wiretap-retro/MigStorm-ITX/Firmware/ARM Firmware/ASB140501/ARM/src/menu.c

/*
Copyright 2005, 2006, 2007 Dennis van Weeren
Copyright 2008, 2009 Jakub Bednarski

This file is part of Minimig

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
You should have received a copy of the GNU General Public License
along with this program.  If not, see <http://www.gnu.org/licenses/>.
*/

// 2009-11-14   - OSD labels changed
// 2009-12-15   - added display of directory name extensions
// 2010-01-09   - support for variable number of tracks
// SB:
// 2014-04-24   - added page wide file list scroll at joystick left/right
// 2014-04-30   - added load of alternative FPGA core .BIN file
// 2014-05-01   - added chipset selection via keyboard shortcut
#include "AT91SAM7S256.h"
#include "stdbool.h"
#include "printf.h"
#include "stringlight.h"
#include "errors.h"
#include "MMC.h"
#include "FAT.h"
#include "OSD.h"
#include "FPGA.h"
#include "FDD.h"
#include "HDD.h"
#include "hardware.h"
#include "firmware.h"
#include "config.h"
#include "menu.h"

// time delay after which file/dir name starts to scroll
#define SCROLL_DELAY 500

unsigned long scroll_offset; // file/dir name scrolling position
unsigned long scroll_timer;  // file/dir name scrolling timer

// other constants
#define DIRSIZE 8 // number of items in directory display window

unsigned char menustate = MENU_NONE1;
unsigned char menusub = 0;
unsigned long menu_timer;


extern unsigned char drives;
extern adfTYPE df[4];

extern configTYPE config;
extern fileTYPE file;
extern char s[40];

extern unsigned char fat32;

extern DIRENTRY DirEntry[MAXDIRENTRIES];
extern unsigned char sort_table[MAXDIRENTRIES];
extern unsigned char nDirEntries;
extern unsigned char iSelectedEntry;
extern unsigned long iCurrentDirectory;
extern char DirEntryLFN[MAXDIRENTRIES][261];
char DirEntryInfo[MAXDIRENTRIES][5]; // disk number info of dir entries
char DiskInfo[5]; // disk number info of selected entry

extern const char version[];

const char *config_filter_msg[] =  {"Disabled", "Hor", "Ver", "Hor+Ver"};
const char *config_memory_chip_msg[] = {"0.5 MB", "1.0 MB", "1.5 MB", "2.0 MB"};
const char *config_memory_slow_msg[] = {"0.0 MB", "0.5 MB", "1.0 MB", "1.5 MB"};
const char *config_scanlines_msg[] = {"VGA alike", "TV  alike", "Cache Off"};

char *config_chipset_msg[] = {"OCS-A500", "OCS-A1000", "ECS", ""};

char *config_autofire_msg[] = {"         AUTOFIRE OFF", "         AUTOFIRE FAST", "         AUTOFIRE MEDIUM", "         AUTOFIRE SLOW"};

extern char UploadKickstart(char *name);
extern unsigned char SaveConfiguration(char *filename);

extern unsigned char DEBUG;

unsigned char config_autofire = 0;

// file selection menu variables
char *fs_pFileExt = NULL;
unsigned char fs_Options;
unsigned char fs_MenuSelect;
unsigned char fs_MenuCancel;

void SelectFile(char* pFileExt, unsigned char Options, unsigned char MenuSelect, unsigned char MenuCancel)
{
    // this function displays file selection menu

    if (strncmp(pFileExt, fs_pFileExt, 3) != 0) // check desired file extension
    { // if different from the current one go to the root directory and init entry buffer
        ChangeDirectory(DIRECTORY_ROOT);
        ScanDirectory(SCAN_INIT, pFileExt, Options);
    }

    fs_pFileExt = pFileExt;
    fs_Options = Options;
    fs_MenuSelect = MenuSelect;
    fs_MenuCancel = MenuCancel;

    menustate = MENU_FILE_SELECT1;
}

void HandleUI(void)
{
    unsigned char i, c, up, down, select, menu, right, left;
    unsigned long len;
    static hardfileTYPE t_hardfile[2]; // temporary copy of former hardfile configuration
    static unsigned char ctrl = false;
    static unsigned char lalt = false;

    // get user control codes
    c = OsdGetCtrl();

    // decode and set events
    menu = false;
    select = false;
    up = false;
    down = false;
    left = false;
    right = false;

    switch (c)
    {
    case KEY_KPPLUS :
        if (ctrl && lalt)
        {
            config.chipset |= CONFIG_TURBO;
            ConfigChipset(config.chipset);
            if (menustate == MENU_SETTINGS_CHIPSET2)
                menustate = MENU_SETTINGS_CHIPSET1;
            else if (menustate == MENU_NONE2 || menustate == MENU_INFO)
                InfoMessage("             TURBO");
        }
        break;
    case KEY_KPMINUS :
        if (ctrl && lalt)
        {
            config.chipset &= ~CONFIG_TURBO;
            ConfigChipset(config.chipset);
            if (menustate == MENU_SETTINGS_CHIPSET2)
                menustate = MENU_SETTINGS_CHIPSET1;
            else if (menustate == MENU_NONE2 || menustate == MENU_INFO)
                InfoMessage("             NORMAL");
        }
        break;
    case KEY_KP0 :
        if (ctrl && lalt)
        {
            if (menustate == MENU_NONE2 || menustate == MENU_INFO)
            {
                config_autofire++;
                config_autofire &= 3;
                ConfigAutofire(config_autofire);
                if (menustate == MENU_NONE2 || menustate == MENU_INFO)
                    InfoMessage(config_autofire_msg[config_autofire]);
            }
        }
        break;
    case KEY_HOME : // chipset selection via keyboard shortcut
        if (ctrl && lalt)
        {
            if (config.chipset & CONFIG_ECS)
               config.chipset &= ~(CONFIG_ECS|CONFIG_A1000);
            else
               config.chipset += CONFIG_A1000;

            ConfigChipset(config.chipset);
            if (menustate == MENU_SETTINGS_CHIPSET2)
                menustate = MENU_SETTINGS_CHIPSET1;
            else if (menustate == MENU_NONE2 || menustate == MENU_INFO)
                 {
                    strcpy(s, "             ");
                    strcat(s, config_chipset_msg[config.chipset >> 2 & 3]);
                    InfoMessage(s);
                 }
         }
        break;
    case KEY_MENU :
        menu = true;
        break;
    case KEY_ESC :
        if (menustate != MENU_NONE2)
            menu = true;
        break;
    case KEY_ENTER :
    case KEY_SPACE :
        select = true;
        break;
    case KEY_UP :
        up = true;
        break;
    case KEY_DOWN :
        down = true;
        break;
    case KEY_LEFT :
        left = true;
        break;
    case KEY_RIGHT :
        right = true;
        break;
    case KEY_CTRL :
        ctrl = true;
        break;
    case KEY_CTRL | KEY_UPSTROKE :
        ctrl = false;
        break;
    case KEY_LALT :
        lalt = true;
        break;
    case KEY_LALT | KEY_UPSTROKE :
        lalt = false;
        break;
    }

    switch (menustate)
    {
        /******************************************************************/
        /* no menu selected                                               */
        /******************************************************************/
    case MENU_NONE1 :

        OsdDisable();
        menustate = MENU_NONE2;
        break;

    case MENU_NONE2 :

        if (menu)
        {
            menustate = MENU_MAIN1;
            menusub = 0;
            OsdClear();
            OsdEnable(DISABLE_KEYBOARD);
        }
        break;

        /******************************************************************/
        /* main menu                                                      */
        /******************************************************************/
    case MENU_MAIN1 :

        OsdWrite(0, "      *** MINIMIG MENU ***   \x15\x11 ", 0);
        OsdWrite(1, "", 0);

        // floppy drive info
        for (i = 0; i < 4; i++)
        {
            if (i <= drives)
            {
                strcpy(s, " DFx: ");
                s[3] = i + '0';
                if (df[i].status & DSK_INSERTED) // floppy disk is inserted
                {
                    strncpy(&s[6], df[i].name, sizeof(df[0].name));
                    strcpy(&s[6 + sizeof(df[0].name)], df[i].status & DSK_WRITABLE ? " RW" : " RO"); // floppy disk is writable or read-only
                }
                else // no floppy disk inserted
                    strcat(s, "* no file *");

                OsdWrite(2 + i, s, menusub == i);
            }
            else
                OsdWrite(2 + i, "", 0);
        }

        OsdWrite(6, "", 0);
        OsdWrite(7, "              Exit", menusub == 4);

        menustate = MENU_MAIN2;
        break;

    case MENU_MAIN2 :

        if (menu)
            menustate = MENU_NONE1;
        else if (up)
        {
            if (menusub > 0)
                menusub--;
            if (menusub > drives)
                menusub = drives;
            menustate = MENU_MAIN1;
        }
        else if (down)
        {
            if (menusub < 4)
                menusub++;
            if (menusub > drives)
                menusub = 4;
            menustate = MENU_MAIN1;
        }
        else if (select)
        {
            if (menusub < 4)
            {
                if (df[menusub].status & DSK_INSERTED) // eject selected floppy
                {
                    df[menusub].status = 0;
                    menustate = MENU_MAIN1;
                }
                else
                {
                    df[menusub].status = 0;
                    SelectFile("ADF", SCAN_DIR | SCAN_LFN, MENU_FILE_SELECTED, MENU_MAIN1);
                }
            }
            else if (menusub == 4)
                menustate = MENU_NONE1;
        }
        else if (c == KEY_BACK) // eject all floppies
        {
            for (i = 0; i <= drives; i++)
                df[i].status = 0;

            menustate = MENU_MAIN1;
        }
        else if (right)
        {
            menustate = MENU_MAIN2_1;
            menusub = 0;
        }
        break;

    case MENU_FILE_SELECTED : // file successfully selected

         InsertFloppy(&df[menusub]);
         menustate = MENU_MAIN1;
         menusub++;
         if (menusub > drives)
             menusub = 4;

         break;

        /******************************************************************/
        /* second part of the main menu                                   */
        /******************************************************************/
    case MENU_MAIN2_1 :

        OsdWrite(0, " \x10\x14   *** MINIMIG MENU ***", 0);
        OsdWrite(1, "", 0);
        OsdWrite(2, "            Reset", menusub == 0);
        OsdWrite(3, "            Settings", menusub == 1);
        OsdWrite(4, "            Firmware", menusub == 2);
        OsdWrite(5, "            FPGA Core", menusub == 3);
        OsdWrite(6, "", 0);
        OsdWrite(7, "              Exit", menusub == 4);

        menustate = MENU_MAIN2_2;
        break;

    case MENU_MAIN2_2 :

        if (menu)
            menustate = MENU_NONE1;
        else if (up)
        {
            if (menusub > 0)
                menusub--;
            menustate = MENU_MAIN2_1;
        }
        else if (down)
        {
            if (menusub < 4)
                menusub++;
            menustate = MENU_MAIN2_1;
        }
        else if (select)
        {
            if (menusub == 0)
            {
                menusub = 1;
                menustate = MENU_RESET1;
            }
            else if (menusub == 1)
            {
                menusub = 0;
                menustate = MENU_SETTINGS1;
            }
            else if (menusub == 2)
            {
                menusub = 2;
                menustate = MENU_FIRMWARE1;
            }
            else if (menusub == 3) // FPGA core file select
            {
                menusub = 3;
                SelectFile("BIN", SCAN_LFN, MENU_COREFILE_SELECTED, MENU_MAIN2_1);
            }
            else if (menusub == 4)
            {
                menusub = 0;
                menustate = MENU_MAIN1;
            }
        }
        else if (left)
        {
            menustate = MENU_MAIN1;
            menusub = 0;
        }
        break;

        /******************************************************************/
        /* core file selected menu                                         */
        /******************************************************************/
    case MENU_COREFILE_SELECTED :

        menusub = 1;

    case MENU_COREFILE_SELECTED1 :

        OsdWrite(0, "", 0);
        OsdWrite(1, "        Upload FPGA Core?", 0);
        OsdWrite(2, "", 0);
        OsdWrite(3, "               Yes", menusub == 0);
        OsdWrite(4, "               No", menusub == 1);
        OsdWrite(5, "", 0);
        OsdWrite(6, "", 0);
        OsdWrite(7, "", 0);

        menustate = MENU_COREFILE_SELECTED2;
        break;

    case MENU_COREFILE_SELECTED2 :

        if (down && menusub < 1)
        {
            menusub++;
            menustate = MENU_COREFILE_SELECTED1;
        }

        if (up && menusub > 0)
        {
            menusub--;
            menustate = MENU_COREFILE_SELECTED1;
        }

        if (select && menusub == 0)
        {
            memcpy((void*)config.corefile.name, (void*)file.name, sizeof(config.corefile.name));
            strcpy(&config.corefile.name[8], "BIN"); // add extension
            ConfigureFpga(config.corefile.name);
        }
        else if ((select && menusub == 1) || menu)
        {
            menusub = 3;
            menustate = MENU_MAIN2_1;
        }

        break;

        /******************************************************************/
        /* file selection menu                                            */
        /******************************************************************/
    case MENU_FILE_SELECT1 :

        PrintDirectory();
        menustate = MENU_FILE_SELECT2;
        break;

    case MENU_FILE_SELECT2 :

        ScrollLongName(); // scrolls file name if longer than display line

        if (c == KEY_HOME)
        {
            ScanDirectory(SCAN_INIT, fs_pFileExt, fs_Options);
            menustate = MENU_FILE_SELECT1;
        }

        if (c == KEY_BACK)
        {
            if (iCurrentDirectory) // if not root directory
            {
                ScanDirectory(SCAN_INIT, fs_pFileExt, fs_Options);
                ChangeDirectory(DirEntry[sort_table[iSelectedEntry]].StartCluster + (fat32 ? (DirEntry[sort_table[iSelectedEntry]].HighCluster & 0x0FFF) << 16 : 0));
                if (ScanDirectory(SCAN_INIT_FIRST, fs_pFileExt, fs_Options))
                    ScanDirectory(SCAN_INIT_NEXT, fs_pFileExt, fs_Options);

                menustate = MENU_FILE_SELECT1;
            }
        }

        if (c == KEY_PGUP || left) // scroll up one page
        {
            ScanDirectory(SCAN_PREV_PAGE, fs_pFileExt, fs_Options);
            menustate = MENU_FILE_SELECT1;
        }

        if (c == KEY_PGDN || right) // scroll down one pge
        {
            ScanDirectory(SCAN_NEXT_PAGE, fs_pFileExt, fs_Options);
            menustate = MENU_FILE_SELECT1;
        }

        if (down) // scroll down one entry
        {
            ScanDirectory(SCAN_NEXT, fs_pFileExt, fs_Options);
            menustate = MENU_FILE_SELECT1;
        }

        if (up) // scroll up one entry
        {
            ScanDirectory(SCAN_PREV, fs_pFileExt, fs_Options);
            menustate = MENU_FILE_SELECT1;
        }

        if ((i = GetASCIIKey(c)))
        { // find an entry beginning with given character
            if (nDirEntries)
            {
                if (DirEntry[sort_table[iSelectedEntry]].Attributes & ATTR_DIRECTORY)
                { // it's a directory
                    if (i < DirEntry[sort_table[iSelectedEntry]].Name[0])
                    {
                        if (!ScanDirectory(i, fs_pFileExt, fs_Options | FIND_FILE))
                            ScanDirectory(i, fs_pFileExt, fs_Options | FIND_DIR);
                    }
                    else if (i > DirEntry[sort_table[iSelectedEntry]].Name[0])
                    {
                        if (!ScanDirectory(i, fs_pFileExt, fs_Options | FIND_DIR))
                            ScanDirectory(i, fs_pFileExt, fs_Options | FIND_FILE);
                    }
                    else
                    {
                        if (!ScanDirectory(i, fs_pFileExt, fs_Options)) // find next
                            if (!ScanDirectory(i, fs_pFileExt, fs_Options | FIND_FILE))
                                ScanDirectory(i, fs_pFileExt, fs_Options | FIND_DIR);
                    }
                }
                else
                { // it's a file
                    if (i < DirEntry[sort_table[iSelectedEntry]].Name[0])
                    {
                        if (!ScanDirectory(i, fs_pFileExt, fs_Options | FIND_DIR))
                            ScanDirectory(i, fs_pFileExt, fs_Options | FIND_FILE);
                    }
                    else if (i > DirEntry[sort_table[iSelectedEntry]].Name[0])
                    {
                        if (!ScanDirectory(i, fs_pFileExt, fs_Options | FIND_FILE))
                            ScanDirectory(i, fs_pFileExt, fs_Options | FIND_DIR);
                    }
                    else
                    {
                        if (!ScanDirectory(i, fs_pFileExt, fs_Options)) // find next
                            if (!ScanDirectory(i, fs_pFileExt, fs_Options | FIND_DIR))
                                ScanDirectory(i, fs_pFileExt, fs_Options | FIND_FILE);
                    }
                }
            }
            menustate = MENU_FILE_SELECT1;
        }

        if (select)
        {
            if (DirEntry[sort_table[iSelectedEntry]].Attributes & ATTR_DIRECTORY)
            {
                ChangeDirectory(DirEntry[sort_table[iSelectedEntry]].StartCluster + (fat32 ? (DirEntry[sort_table[iSelectedEntry]].HighCluster & 0x0FFF) << 16 : 0));
                {
                    if (strncmp((char*)DirEntry[sort_table[iSelectedEntry]].Name, "..", 2) == 0)
                    { // parent dir selected
                         if (ScanDirectory(SCAN_INIT_FIRST, fs_pFileExt, fs_Options))
                             ScanDirectory(SCAN_INIT_NEXT, fs_pFileExt, fs_Options);
                         else
                             ScanDirectory(SCAN_INIT, fs_pFileExt, fs_Options);
                    }
                    else
                        ScanDirectory(SCAN_INIT, fs_pFileExt, fs_Options);

                    menustate = MENU_FILE_SELECT1;
                }
            }
            else
            {
                if (nDirEntries)
                {
                    file.long_name[0] = 0;
                    len = strlen(DirEntryLFN[sort_table[iSelectedEntry]]);
                    if (len > 4)
                        if (DirEntryLFN[sort_table[iSelectedEntry]][len-4] == '.')
                            len -= 4; // remove extension

                    if (len > sizeof(file.long_name))
                        len = sizeof(file.long_name);

                    strncpy(file.name, (const char*)DirEntry[sort_table[iSelectedEntry]].Name, sizeof(file.name));
                    memset(file.long_name, 0, sizeof(file.long_name));
                    strncpy(file.long_name, DirEntryLFN[sort_table[iSelectedEntry]], len);
                    strncpy(DiskInfo, DirEntryInfo[iSelectedEntry], sizeof(DiskInfo));

                    file.size = DirEntry[sort_table[iSelectedEntry]].FileSize;
                    file.attributes = DirEntry[sort_table[iSelectedEntry]].Attributes;
                    file.start_cluster = DirEntry[sort_table[iSelectedEntry]].StartCluster + (fat32 ? (DirEntry[sort_table[iSelectedEntry]].HighCluster & 0x0FFF) << 16 : 0);
                    file.cluster = file.start_cluster;
                    file.sector = 0;

                    menustate = fs_MenuSelect;
                }
            }
        }

        if (menu)
        {
            menustate = fs_MenuCancel;
        }

        break;

        /******************************************************************/
        /* reset menu                                                     */
        /******************************************************************/
    case MENU_RESET1 :

        OsdWrite(0, "", 0);
        OsdWrite(1, "         Reset Minimig?", 0);
        OsdWrite(2, "", 0);
        OsdWrite(3, "               Yes", menusub == 0);
        OsdWrite(4, "               No", menusub == 1);
        OsdWrite(5, "", 0);
        OsdWrite(6, "", 0);
        OsdWrite(7, "", 0);

        menustate = MENU_RESET2;
        break;

    case MENU_RESET2 :

        if (down && menusub < 1)
        {
            menusub++;
            menustate = MENU_RESET1;
        }

        if (up && menusub > 0)
        {
            menusub--;
            menustate = MENU_RESET1;
        }

        if (select && menusub == 0)
        {
            menustate = MENU_NONE1;
            OsdReset(RESET_NORMAL);
        }

        if (menu || (select && menusub == 1)) // exit menu
        {
            menustate = MENU_MAIN2_1;
            menusub = 0;
        }
        break;

        /******************************************************************/
        /* settings menu                                                  */
        /******************************************************************/
    case MENU_SETTINGS1 :

        OsdWrite(0, "         ** SETTINGS **", 0);
        OsdWrite(1, "", 0);
        OsdWrite(2, "             Chipset", menusub == 0);
        OsdWrite(3, "             Memory", menusub == 1);
        OsdWrite(4, "             Drives", menusub == 2);
        OsdWrite(5, "             Video", menusub == 3);
        OsdWrite(6, "", 0);

        if (menusub == 5)
            OsdWrite(7, "  \x12           Save           \x12", 1);
        else if (menusub == 4)
            OsdWrite(7, "  \x13           Exit           \x13", 1);
        else
            OsdWrite(7, "              Exit", 0);

        menustate = MENU_SETTINGS2;
        break;

    case MENU_SETTINGS2 :

        if (down && menusub < 5)
        {
            menusub++;
            menustate = MENU_SETTINGS1;
        }

        if (up && menusub > 0)
        {
            menusub--;
            menustate = MENU_SETTINGS1;
        }

        if (select)
        {
            if (menusub == 0)
            {
                menustate = MENU_SETTINGS_CHIPSET1;
                menusub = 0;
            }
            else if (menusub == 1)
            {
                menustate = MENU_SETTINGS_MEMORY1;
                menusub = 0;
            }
            else if (menusub == 2)
            {
                menustate = MENU_SETTINGS_DRIVES1;
                menusub = 0;
            }
            else if (menusub == 3)
            {
                menustate = MENU_SETTINGS_VIDEO1;
                menusub = 0;
            }
            else if (menusub == 4)
            {
                menustate = MENU_MAIN2_1;
                menusub = 1;
            }
            else if (menusub == 5)
            {
                SaveConfiguration("MINIMIG CFG");
                menustate = MENU_MAIN2_1;
                menusub = 1;
            }
        }

        if (menu)
        {
            menustate = MENU_MAIN2_1;
            menusub = 1;
        }
        break;

        /******************************************************************/
        /* chipset settings menu                                          */
        /******************************************************************/
    case MENU_SETTINGS_CHIPSET1 :

        OsdWrite(0, " \x10\x14         CHIPSET          \x15\x11", 0);
        OsdWrite(1, "", 0);
        strcpy(s, "            CPU : ");
        strcat(s, config.chipset & CONFIG_TURBO ? "Turbo" : "Normal");
        OsdWrite(2, s, menusub == 0);
        strcpy(s, "          Video : ");
        strcat(s, config.chipset & CONFIG_NTSC ? "NTSC" : "PAL");
        OsdWrite(3, s, menusub == 1);
        strcpy(s, "        Chipset : ");
        strcat(s, config_chipset_msg[config.chipset >> 2 & 3]);
        OsdWrite(4, s, menusub == 2);
        OsdWrite(5, "", 0);
        OsdWrite(6, "", 0);
        OsdWrite(7, "              Exit", menusub == 3);

        menustate = MENU_SETTINGS_CHIPSET2;
        break;

    case MENU_SETTINGS_CHIPSET2 :

        if (down && menusub < 3)
        {
            menusub++;
            menustate = MENU_SETTINGS_CHIPSET1;
        }

        if (up && menusub > 0)
        {
            menusub--;
            menustate = MENU_SETTINGS_CHIPSET1;
        }

        if (select)
        {
            if (menusub == 0)
            {
                config.chipset ^= CONFIG_TURBO;
                menustate = MENU_SETTINGS_CHIPSET1;
                ConfigChipset(config.chipset);
            }
            else if (menusub == 1)
            {
                config.chipset ^= CONFIG_NTSC;
                menustate = MENU_SETTINGS_CHIPSET1;
                ConfigChipset(config.chipset);
            }
            else if (menusub == 2)
            {
                if (config.chipset & CONFIG_ECS)
                   config.chipset &= ~(CONFIG_ECS|CONFIG_A1000);
                else
                    config.chipset += CONFIG_A1000;

                menustate = MENU_SETTINGS_CHIPSET1;
                ConfigChipset(config.chipset);
            }
            else if (menusub == 3)
            {
                menustate = MENU_SETTINGS1;
                menusub = 0;
            }
        }

        if (menu)
        {
            menustate = MENU_SETTINGS1;
            menusub = 0;
        }
        else if (right)
        {
            menustate = MENU_SETTINGS_MEMORY1;
            menusub = 0;
        }
        else if (left)
        {
            menustate = MENU_SETTINGS_VIDEO1;
            menusub = 0;
        }
        break;

        /******************************************************************/
        /* memory settings menu                                           */
        /******************************************************************/
    case MENU_SETTINGS_MEMORY1 :

        OsdWrite(0, " \x10\x14          MEMORY          \x15\x11", 0);
        OsdWrite(1, "", 0);
        strcpy(s, "        CHIP : ");
        strcat(s, config_memory_chip_msg[config.memory & 0x03]);
        OsdWrite(2, s, menusub == 0);
        strcpy(s, "        SLOW : ");
        strcat(s, config_memory_slow_msg[config.memory >> 2 & 0x03]);
        OsdWrite(3, s, menusub == 1);
        strcpy(s, "        ROM  : ");
        if (config.kickstart.long_name[0])
            strncat(s, config.kickstart.long_name, sizeof(config.kickstart.long_name));
        else
            strncat(s, config.kickstart.name, sizeof(config.kickstart.name));
        OsdWrite(4, s, menusub == 2);
        strcpy(s, "        AR3  : ");
        strcat(s, config.disable_ar3 ? "Disabled" : "Enabled");
        OsdWrite(5, s, menusub == 3);
        OsdWrite(6, "", 0);
        OsdWrite(7, "              Exit", menusub == 4);

        menustate = MENU_SETTINGS_MEMORY2;
        break;

    case MENU_SETTINGS_MEMORY2 :

        if (down && menusub < 4)
        {
            menusub++;
            menustate = MENU_SETTINGS_MEMORY1;
        }

        if (up && menusub > 0)
        {
            menusub--;
            menustate = MENU_SETTINGS_MEMORY1;
        }

        if (select)
        {
            if (menusub == 0)
            {
                config.memory = ((config.memory + 1) & 0x03) | (config.memory & ~0x03);
                menustate = MENU_SETTINGS_MEMORY1;
                ConfigMemory(config.memory);
            }
            else if (menusub == 1)
            {
                config.memory = ((config.memory + 4) & 0x0C) | (config.memory & ~0x0C);
                menustate = MENU_SETTINGS_MEMORY1;
                ConfigMemory(config.memory);
            }
            else if (menusub == 2)
            {
                SelectFile("ROM", SCAN_LFN, MENU_ROMFILE_SELECTED, MENU_SETTINGS_MEMORY1);
            }
            else if (menusub == 3)
            {
                config.disable_ar3 ^= 0x01;
                config.disable_ar3 &= 0x01;
                menustate = MENU_SETTINGS_MEMORY1;
            }
            else if (menusub == 4)
            {
                menustate = MENU_SETTINGS1;
                menusub = 1;
            }
        }

        if (menu)
        {
            menustate = MENU_SETTINGS1;
            menusub = 1;
        }
        else if (right)
        {
            menustate = MENU_SETTINGS_DRIVES1;
            menusub = 0;
        }
        else if (left)
        {
            menustate = MENU_SETTINGS_CHIPSET1;
            menusub = 0;
        }
        break;

        /******************************************************************/
        /* drive settings menu                                            */
        /******************************************************************/
    case MENU_SETTINGS_DRIVES1 :

        OsdWrite(0, " \x10\x14          DRIVES          \x15\x11", 0);
        OsdWrite(1, "", 0);
        sprintf(s, "         Drives : %d", config.floppy.drives + 1);
        OsdWrite(2, s, menusub == 0);
        strcpy(s,  "          Speed : ");
        strcat(s, config.floppy.speed ? "Fast" : "Normal");
        OsdWrite(3, s, menusub == 1);
        strcpy(s,  "       A600 IDE : ");
        strcat(s, config.enable_ide ? "Enabled" : "Disabled");
        OsdWrite(4, s, menusub == 2);
        sprintf(s, "      Hardfiles : %d", (config.hardfile[0].present & config.hardfile[0].enabled) + (config.hardfile[1].present & config.hardfile[1].enabled));
        OsdWrite(5,s, menusub == 3);
        OsdWrite(6, "", 0);
        OsdWrite(7, "              Exit", menusub == 4);

        menustate = MENU_SETTINGS_DRIVES2;
        break;

    case MENU_SETTINGS_DRIVES2 :

        if (down && menusub < 4)
        {
            menusub++;
            menustate = MENU_SETTINGS_DRIVES1;
        }

        if (up && menusub > 0)
        {
            menusub--;
            menustate = MENU_SETTINGS_DRIVES1;
        }

        if (select)
        {
            if (menusub == 0)
            {
                config.floppy.drives++;
                config.floppy.drives &= 0x03;
                menustate = MENU_SETTINGS_DRIVES1;
                ConfigFloppy(config.floppy.drives, config.floppy.speed);
            }
            else if (menusub == 1)
            {
                config.floppy.speed++;
                config.floppy.speed &= 0x01;
                menustate = MENU_SETTINGS_DRIVES1;
                ConfigFloppy(config.floppy.drives, config.floppy.speed);
            }
            else if (menusub == 2)
            {
                config.enable_ide ^= 0x01;
                menustate = MENU_SETTINGS_DRIVES1;
                ConfigIDE(config.enable_ide, config.hardfile[0].present & config.hardfile[0].enabled, config.hardfile[1].present & config.hardfile[1].enabled);
            }
            else if (menusub == 3)
            {
                t_hardfile[0] = config.hardfile[0];
                t_hardfile[1] = config.hardfile[1];
                menustate = MENU_SETTINGS_HARDFILE1;
                menusub = 4;
            }
            else if (menusub == 4)
            {
                menustate = MENU_SETTINGS1;
                menusub = 2;
            }
        }

        if (menu)
        {
            menustate = MENU_SETTINGS1;
            menusub = 2;
        }
        else if (right)
        {
            menustate = MENU_SETTINGS_VIDEO1;
            menusub = 0;
        }
        else if (left)
        {
            menustate = MENU_SETTINGS_MEMORY1;
            menusub = 0;
        }
        break;

        /******************************************************************/
        /* hardfile settings menu                                         */
        /******************************************************************/
    case MENU_SETTINGS_HARDFILE1 :

        OsdWrite(0, "            HARDFILES", 0);
        OsdWrite(1, "", 0);
        strcpy(s, "     Master : ");
        strcat(s, config.hardfile[0].present ? config.hardfile[0].enabled ? "Enabled" : "Disabled" : "Undefined");
        OsdWrite(2, s, menusub == 0);
        if (config.hardfile[0].present)
        {
            strcpy(s, "                                ");
            if (config.hardfile[0].long_name[0])
                strncpy(&s[14], config.hardfile[0].long_name, sizeof(config.hardfile[0].long_name));
            else
                strncpy(&s[14], config.hardfile[0].name, sizeof(config.hardfile[0].name));
            OsdWrite(3, s, menusub == 1);
        }
        else
            OsdWrite(3, "              * no file *", menusub == 1);

        strcpy(s, "     Slave  : ");
        strcat(s, config.hardfile[1].present ? config.hardfile[1].enabled ? "Enabled" : "Disabled" : "Undefined");
        OsdWrite(4, s, menusub == 2);
        if (config.hardfile[1].present)
        {
            strcpy(s, "                                ");
            if (config.hardfile[1].long_name[0])
                strncpy(&s[14], config.hardfile[1].long_name, sizeof(config.hardfile[0].long_name));
            else
                strncpy(&s[14], config.hardfile[1].name, sizeof(config.hardfile[0].name));
            OsdWrite(5, s, menusub == 3);
        }
        else
            OsdWrite(5, "              * no file *", menusub == 3);

        OsdWrite(6, "", 0);
        OsdWrite(7, "              Exit", menusub == 4);

        menustate = MENU_SETTINGS_HARDFILE2;
        break;

    case MENU_SETTINGS_HARDFILE2 :

        if (down && menusub < 4)
        {
            menusub++;
            menustate = MENU_SETTINGS_HARDFILE1;
        }

        if (up && menusub > 0)
        {
            menusub--;
            menustate = MENU_SETTINGS_HARDFILE1;
        }

        if (select)
        {
            if (menusub == 0)
            {
                if (config.hardfile[0].present)
                {
                   config.hardfile[0].enabled ^= 0x01;
                   menustate = MENU_SETTINGS_HARDFILE1;
                }
            }
            else if (menusub == 1)
            {
                SelectFile("HDF", SCAN_LFN, MENU_HARDFILE_SELECTED, MENU_SETTINGS_HARDFILE1);
            }
            else if (menusub == 2)
            {
                if (config.hardfile[1].present)
                {
                   config.hardfile[1].enabled ^= 0x01;
                   menustate = MENU_SETTINGS_HARDFILE1;
                }
            }
            else if (menusub == 3)
            {
                SelectFile("HDF", SCAN_LFN, MENU_HARDFILE_SELECTED, MENU_SETTINGS_HARDFILE1);
            }
            else if (menusub == 4) // return to previous menu
            {
                menustate = MENU_HARDFILE_EXIT;
            }
        }

        if (menu) // return to previous menu
        {
            menustate = MENU_HARDFILE_EXIT;
        }
        break;

        /******************************************************************/
        /* hardfile selected menu                                         */
        /******************************************************************/
    case MENU_HARDFILE_SELECTED :

        if (menusub == 1) // master drive selected
        {
            memcpy((void*)config.hardfile[0].name, (void*)file.name, sizeof(config.hardfile[0].name));
            memcpy((void*)config.hardfile[0].long_name, (void*)file.long_name, sizeof(config.hardfile[0].long_name));
            config.hardfile[0].present = 1;
        }

        if (menusub == 3) // slave drive selected
        {
            memcpy((void*)config.hardfile[1].name, (void*)file.name, sizeof(config.hardfile[1].name));
            memcpy((void*)config.hardfile[1].long_name, (void*)file.long_name, sizeof(config.hardfile[1].long_name));
            config.hardfile[1].present = 1;
        }

        menustate = MENU_SETTINGS_HARDFILE1;
        break;

     // check if hardfile configuration has changed
    case MENU_HARDFILE_EXIT :

         if (memcmp(config.hardfile, t_hardfile, sizeof(t_hardfile)) != 0)
         {
             menustate = MENU_HARDFILE_CHANGED1;
             menusub = 1;
         }
         else
         {
             menustate = MENU_SETTINGS_DRIVES1;
             menusub = 3;
         }

         break;

    // hardfile configuration has changed, ask user if he wants to use the new settings
    case MENU_HARDFILE_CHANGED1 :

        OsdWrite(0, "", 0);
        OsdWrite(1, "      Changing configuration", 0);
        OsdWrite(2, "        requires reset.", 0);
        OsdWrite(3, "", 0);
        OsdWrite(4, "         Reset Minimig?", 0);
        OsdWrite(5, "", 0);
        OsdWrite(6, "               Yes", menusub == 0);
        OsdWrite(7, "               No", menusub == 1);

        menustate = MENU_HARDFILE_CHANGED2;
        break;

    case MENU_HARDFILE_CHANGED2 :

        if (down && menusub < 1)
        {
            menusub++;
            menustate = MENU_HARDFILE_CHANGED1;
        }

        if (up && menusub > 0)
        {
            menusub--;
            menustate = MENU_HARDFILE_CHANGED1;
        }

        if (select)
        {
            if (menusub == 0) // yes
            {
                if (strncmp(config.hardfile[0].name, t_hardfile[0].name, sizeof(t_hardfile[0].name)) != 0)
                    OpenHardfile(0);

                if (strncmp(config.hardfile[1].name, t_hardfile[1].name, sizeof(t_hardfile[1].name)) != 0)
                    OpenHardfile(1);

                ConfigIDE(config.enable_ide, config.hardfile[0].present & config.hardfile[0].enabled, config.hardfile[1].present & config.hardfile[1].enabled);
                menustate = MENU_NONE1;
                OsdReset(RESET_NORMAL);
            }
            else if (menusub == 1) // no
            {
                memcpy(config.hardfile, t_hardfile, sizeof(t_hardfile)); // restore configuration
                menustate = MENU_SETTINGS_DRIVES1;
                menusub = 3;
            }
        }

        if (menu)
        {
            memcpy(config.hardfile, t_hardfile, sizeof(t_hardfile)); // restore configuration
            menustate = MENU_SETTINGS_DRIVES1;
            menusub = 3;
        }
        break;

        /******************************************************************/
        /* video settings menu                                            */
        /******************************************************************/
    case MENU_SETTINGS_VIDEO1 :

        OsdWrite(0, " \x10\x14          VIDEO           \x15\x11", 0);
        OsdWrite(1, "", 0);
        strcpy(s, "   Lores Filter : ");
        strcat(s, config_filter_msg[config.filter.lores]);
        OsdWrite(2, s, menusub == 0);
        strcpy(s, "   Hires Filter : ");
        strcat(s, config_filter_msg[config.filter.hires]);
        OsdWrite(3, s, menusub == 1);
        strcpy(s, "   Scanlines    : ");
        strcat(s, config_scanlines_msg[config.scanlines]);
        OsdWrite(4, s, menusub == 2);
        OsdWrite(5, "", 0);
        OsdWrite(6, "", 0);
        OsdWrite(7, "              Exit", menusub == 3);

        menustate = MENU_SETTINGS_VIDEO2;
        break;

    case MENU_SETTINGS_VIDEO2 :

        if (down && menusub < 3)
        {
            menusub++;
            menustate = MENU_SETTINGS_VIDEO1;
        }

        if (up && menusub > 0)
        {
            menusub--;
            menustate = MENU_SETTINGS_VIDEO1;
        }

        if (select)
        {
            if (menusub == 0)
            {
                config.filter.lores++;
                config.filter.lores &= 0x03;
                menustate = MENU_SETTINGS_VIDEO1;
                ConfigFilter(config.filter.lores, config.filter.hires);
            }
            else if (menusub == 1)
            {
                config.filter.hires++;
                config.filter.hires &= 0x03;
                menustate = MENU_SETTINGS_VIDEO1;
                ConfigFilter(config.filter.lores, config.filter.hires);
            }
            else if (menusub == 2)
            {
                config.scanlines++;
                if (config.scanlines > 2)
                    config.scanlines = 0;
                menustate = MENU_SETTINGS_VIDEO1;
                ConfigScanlines(config.scanlines);
            }
            else if (menusub == 3)
            {
                menustate = MENU_SETTINGS1;
                menusub = 3;
            }
        }

        if (menu)
        {
            menustate = MENU_SETTINGS1;
            menusub = 3;
        }
        else if (right)
        {
            menustate = MENU_SETTINGS_CHIPSET1;
            menusub = 0;
        }
        else if (left)
        {
            menustate = MENU_SETTINGS_DRIVES1;
            menusub = 0;
        }
        break;

        /******************************************************************/
        /* rom file selected menu                                         */
        /******************************************************************/
    case MENU_ROMFILE_SELECTED :

         menusub = 1;
         // no break intended

    case MENU_ROMFILE_SELECTED1 :

        OsdWrite(0, "", 0);
        OsdWrite(1, "        Reload Kickstart?", 0);
        OsdWrite(2, "", 0);
        OsdWrite(3, "               Yes", menusub == 0);
        OsdWrite(4, "               No", menusub == 1);
        OsdWrite(5, "", 0);
        OsdWrite(6, "", 0);
        OsdWrite(7, "", 0);

        menustate = MENU_ROMFILE_SELECTED2;
        break;

    case MENU_ROMFILE_SELECTED2 :

        if (down && menusub < 1)
        {
            menusub++;
            menustate = MENU_ROMFILE_SELECTED1;
        }

        if (up && menusub > 0)
        {
            menusub--;
            menustate = MENU_ROMFILE_SELECTED1;
        }

        if (select)
        {
            if (menusub == 0)
            {
                memcpy((void*)config.kickstart.name, (void*)file.name, sizeof(config.kickstart.name));
                memcpy((void*)config.kickstart.long_name, (void*)file.long_name, sizeof(config.kickstart.long_name));

                OsdDisable();
                OsdReset(RESET_BOOTLOADER);
                ConfigChipset(config.chipset | CONFIG_TURBO);
                ConfigFloppy(config.floppy.drives, CONFIG_FLOPPY2X);
                if (UploadKickstart(config.kickstart.name))
                {
                    BootExit();
                }
                ConfigChipset(config.chipset); // restore CPU speed mode
                ConfigFloppy(config.floppy.drives, config.floppy.speed); // restore floppy speed mode

                menustate = MENU_NONE1;
            }
            else if (menusub == 1)
            {
                menustate = MENU_SETTINGS_MEMORY1;
                menusub = 2;
            }
        }

        if (menu)
        {
            menustate = MENU_SETTINGS_MEMORY1;
            menusub = 2;
        }
        break;
//         ConfigureFpga("MINIMIG2BIN");

        /******************************************************************/
        /* firmware menu */
        /******************************************************************/
    case MENU_FIRMWARE1 :

        OsdWrite(0, "         ** FIRMWARE **", 0);
        OsdWrite(1, "", 0);
        sprintf(s, "   Running ARM fw: %s", version + 5);
        OsdWrite(2, s, 0);
        OsdWrite(3, "", 0);
        OsdWrite(4, "            SD-Update", menusub == 0);
        OsdWrite(5, "             Options", menusub == 1);
        OsdWrite(6, "", 0);
        OsdWrite(7, "              Exit", menusub == 2);

        menustate = MENU_FIRMWARE2;
        break;

    case MENU_FIRMWARE2 :

        if (menu)
        {
            menusub = 2;
            menustate = MENU_MAIN2_1;
        }
        else if (up)
        {
            if (menusub > 0)
                menusub--;
            menustate = MENU_FIRMWARE1;
        }
        else if (down)
        {
            if (menusub < 2)
                menusub++;
            menustate = MENU_FIRMWARE1;
        }
        else if (select)
        {
            if (menusub == 0)
            {
                if (CheckFirmware(&file, "FIRMWAREUPG"))
                    menustate = MENU_FIRMWARE_UPDATE1;
                else
                    menustate = MENU_FIRMWARE_UPDATE_ERROR1;
                menusub = 1;
                OsdClear();
            }
            else if (menusub == 1)
            {
                menustate = MENU_FIRMWARE_OPTIONS1;
                menusub = 1;
                OsdClear();
            }
            else if (menusub == 2)
            {
                menustate = MENU_MAIN2_1;
                menusub = 2;
            }
        }
        break;

        /******************************************************************/
        /* firmware update message menu */
        /******************************************************************/
    case MENU_FIRMWARE_UPDATE1 :

        OsdWrite(2, "          Are you sure?", 0);

        OsdWrite(6, "               Yes", menusub == 0);
        OsdWrite(7, "               No", menusub == 1);

        menustate = MENU_FIRMWARE_UPDATE2;
        break;

    case MENU_FIRMWARE_UPDATE2 :

        if (down && menusub < 1)
        {
            menusub++;
            menustate = MENU_FIRMWARE_UPDATE1;
        }

        if (up && menusub > 0)
        {
            menusub--;
            menustate = MENU_FIRMWARE_UPDATE1;
        }

        if (select)
        {
            if (menusub == 0)
            {
                menustate = MENU_FIRMWARE_UPDATING1;
                menusub = 0;
                OsdClear();
            }
            else if (menusub == 1)
            {
                menustate = MENU_FIRMWARE1;
                menusub = 2;
            }
        }
        break;

        /******************************************************************/
        /* firmware update in progress message menu*/
        /******************************************************************/
    case MENU_FIRMWARE_UPDATING1 :
        OsdWrite(1, "        Updating firmware", 0);
        OsdWrite(3, "           Please wait", 0);
        menustate = MENU_FIRMWARE_UPDATING2;
        break;

    case MENU_FIRMWARE_UPDATING2 :

        WriteFirmware(&file);
        Error = ERROR_UPDATE_FAILED;
        menustate = MENU_FIRMWARE_UPDATE_ERROR1;
        menusub = 0;
        OsdClear();
        break;

        /******************************************************************/
        /* firmware update error message menu*/
        /******************************************************************/
    case MENU_FIRMWARE_UPDATE_ERROR1 :

        switch (Error)
        {
        case ERROR_FILE_NOT_FOUND :
            OsdWrite(1, "          Update file", 0);
            OsdWrite(2, "           not found!", 0);
            break;

        case ERROR_INVALID_DATA :
            OsdWrite(1, "            Invalid ", 0);
            OsdWrite(2, "          update file!", 0);
            break;

        case ERROR_UPDATE_FAILED :
            OsdWrite(1, "         Update failed!", 0);
            OsdWrite(2, "    Dont panic! Flash ARM via", 0);
            OsdWrite(3, "    USB and SAM-BA/PROG Tool!", 0);
            break;
        }
            OsdWrite(7, "                OK", menusub == 0);
        menustate = MENU_FIRMWARE_UPDATE_ERROR2;
        break;

    case MENU_FIRMWARE_UPDATE_ERROR2 :

        if (select)
        {
            menustate = MENU_FIRMWARE1;
            menusub = 2;
        }
        break;

        /******************************************************************/
        /* firmware options menu */
        /******************************************************************/
    case MENU_FIRMWARE_OPTIONS1 :

        OsdWrite(0, "          ** OPTIONS **", 0);

        if (GetSPIMode() == SPIMODE_FAST)
        {
            OsdWrite(2, "      Fast SPI is enabled", menusub == 0);

            OsdWrite(4, "    Hold MENU button while", 0);
            OsdWrite(5, "    powering-on to disable it.", 0);
        }
        else
            OsdWrite(2, "        Enable Fast SPI ", menusub == 0);

            OsdWrite(7, "              Exit", menusub == 1);

        menustate = MENU_FIRMWARE_OPTIONS2;
        break;

    case MENU_FIRMWARE_OPTIONS2 :

        if (c == KEY_F8)
        {
            if (DEBUG)
            {
                DEBUG = 0;
                printf("DEBUG OFF\r");
            }
            else
            {
                DEBUG = 1;
                printf("DEBUG ON\r");
            }
        }
        else if (menu)
        {
            menusub = 1;
            menustate = MENU_FIRMWARE1;
        }
        else if (up)
        {
            if (menusub > 0  && GetSPIMode() != SPIMODE_FAST)
                menusub--;

            menustate = MENU_FIRMWARE_OPTIONS1;
        }
        else if (down)
        {
            if (menusub < 1)
                menusub++;
            menustate = MENU_FIRMWARE_OPTIONS1;
        }
        else if (select)
        {
            if (menusub == 0)
            {
                menusub = 1;
                menustate = MENU_FIRMWARE_OPTIONS_ENABLE1;
                OsdClear();
            }
            else if (menusub == 1)
            {
                menusub = 1;
                menustate = MENU_FIRMWARE1;
            }
        }
        break;

        /******************************************************************/
        /* SPI high speed mode enable message menu*/
        /******************************************************************/
    case MENU_FIRMWARE_OPTIONS_ENABLE1 :

        OsdWrite(0, "    Enabling fast SPI without", 0);
        OsdWrite(1, "      hardware modification", 0);
        OsdWrite(2, "          will be fatal!", 0);
        OsdWrite(4, "             Enable?", 0);
        OsdWrite(6, "               Yes", menusub == 0);
        OsdWrite(7, "               No", menusub == 1);

        menustate = MENU_FIRMWARE_OPTIONS_ENABLE2;
        break;

    case MENU_FIRMWARE_OPTIONS_ENABLE2 :

        if (down && menusub < 1)
        {
            menusub++;
            menustate = MENU_FIRMWARE_OPTIONS_ENABLE1;
        }

        if (up && menusub > 0)
        {
            menusub--;
            menustate = MENU_FIRMWARE_OPTIONS_ENABLE1;
        }

        if (select)
        {
            if (menusub == 0)
            {
                SetSPIMode(SPIMODE_FAST);
                menustate = MENU_FIRMWARE_OPTIONS_ENABLED1;
                menusub = 0;
                OsdClear();
            }
            else if (menusub == 1)
            {
                menustate = MENU_FIRMWARE_OPTIONS1;
                menusub = 0;
                OsdClear();
            }
        }
        break;

        /******************************************************************/
        /* SPI high speed mode enabled message menu*/
        /******************************************************************/
    case MENU_FIRMWARE_OPTIONS_ENABLED1 :

        OsdWrite(1, "    Fast SPI mode will be", 0);
        OsdWrite(2, "    activated after restart.", 0);
        OsdWrite(3, "    Hold MENU button while", 0);
        OsdWrite(4, "    powering-on to disable it.", 0);

        OsdWrite(7, "                OK", menusub == 0);

        menustate = MENU_FIRMWARE_OPTIONS_ENABLED2;
        break;

    case MENU_FIRMWARE_OPTIONS_ENABLED2 :

        if (select)
        {
            menustate = MENU_NONE1;
            menusub = 0;
            OsdClear();
        }
        break;

        /******************************************************************/
        /* error message menu                                             */
        /******************************************************************/
    case MENU_ERROR :

        if (menu)
            menustate = MENU_MAIN1;

        break;

        /******************************************************************/
        /* popup info menu                                                */
        /******************************************************************/
    case MENU_INFO :

        if (menu)
            menustate = MENU_MAIN1;
        else if (CheckTimer(menu_timer))
            menustate = MENU_NONE1;

        break;

        /******************************************************************/
        /* we should never come here                                      */
        /******************************************************************/
    default :

        break;
    }
}

void ScrollLongName(void)
{
// this function is called periodically when file selection window is displayed
// it checks if predefined period of time has elapsed and scrolls the name if necessary

    #define BLANKSPACE 10 // number of spaces between the end and start of repeated name

    long offset;
    long len;
    long max_len;
    // char k = sort_table[iSelectedEntry];
    unsigned short  k = sort_table[iSelectedEntry];
    static unsigned long pioa_old;
    unsigned long pioa;

    pioa = *AT91C_PIOA_PDSR;

    if (DirEntryLFN[k][0] && CheckTimer(scroll_timer)) // scroll if long name and timer delay elapsed
    if ((pioa ^ pioa_old) & INIT_B)
    {
        scroll_timer = GetTimer(0); // reset scroll timer to repeat delay

        scroll_offset++; // increase scroll position (2 pixel unit)
        memset(s, ' ', 32); // clear buffer

        len = strlen(DirEntryLFN[k]); // get name length

        if (len > 4)
            if (DirEntryLFN[k][len - 4] == '.')
                len -= 4; // remove extension

        if (len > 30) // scroll name if longer than display size
        {
            if (scroll_offset >= (len + BLANKSPACE) << 2) // reset scroll position if it exceeds predefined maximum
                scroll_offset = 0;

            offset = scroll_offset >> 2; // get new starting character of the name (scroll_offset is in 2 pixel unit)

            len -= offset; // remaing number of characters in the name

            max_len = 31; // number of file name characters to display (one more required for srolling)
            if (DirEntry[k].Attributes & ATTR_DIRECTORY)
                max_len = 25; // number of directory name characters to display

            if (len > max_len)
                len = max_len; // trim length to the maximum value

            if (len > 0)
                strncpy(s, &DirEntryLFN[k][offset], len); // copy name substring

            if (len < max_len - BLANKSPACE) // file name substring and blank space is shorter than display line size
                strncpy(s + len + BLANKSPACE, &DirEntryLFN[k][0], max_len - len - BLANKSPACE); // repeat the name after its end and predefined number of blank space

            OSD_PrintText((unsigned char)iSelectedEntry, s, 8, (max_len - 1) << 3, (scroll_offset & 0x3) << 1, 1); // OSD print function with pixel precision
        }
    }
    pioa_old = pioa;
}

char* GetDiskInfo(char* lfn, long len)
{
// extracts disk number substring form file name
// if file name contains "X of Y" substring where X and Y are one or two digit number
// then the number substrings are extracted and put into the temporary buffer for further processing
// comparision is case sensitive

    short i, k;
    static char info[] = "XX/XX"; // temporary buffer
    static char template[4] = " of "; // template substring to search for
    char *ptr1, *ptr2, c;
    unsigned char cmp;

    if (len > 20) // scan only names which can't be fully displayed
    {
        for (i = (unsigned short)len - 1 - sizeof(template); i > 0; i--) // scan through the file name starting from its end
        {
            ptr1 = &lfn[i]; // current start position
            ptr2 = template;
            cmp = 0;
            for (k = 0; k < sizeof(template); k++) // scan through template
            {
                cmp |= *ptr1++ ^ *ptr2++; // compare substrings' characters one by one
                if (cmp)
                   break; // stop further comparing if difference already found
            }

            if (!cmp) // match found
            {
                k = i - 1; // no need to check if k is valid since i is greater than zero
                c = lfn[k]; // get the first character to the left of the matched template substring
                if (c >= '0' && c <= '9') // check if a digit
                {
                    info[1] = c; // copy to buffer
                    info[0] = ' '; // clear previous character
                    k--; // go to the preceding character
                    if (k >= 0) // check if index is valid
                    {
                        c = lfn[k];
                        if (c >= '0' && c <= '9') // check if a digit
                            info[0] = c; // copy to buffer
                    }

                    k = i + sizeof(template); // get first character to the right of the mached template substring
                    c = lfn[k]; // no need to check if index is valid
                    if (c >= '0' && c <= '9') // check if a digit
                    {
                        info[3] = c; // copy to buffer
                        info[4] = ' '; // clear next char
                        k++; // go to the followwing character
                        if (k < len) // check if index is valid
                        {
                            c = lfn[k];
                            if (c >= '0' && c <= '9') // check if a digit
                                info[4] = c; // copy to buffer
                        }
                        return info;
                    }
                }
            }
        }
    }
    return NULL;
}

// print directory contents
void PrintDirectory(void)
{
    unsigned char i;
    unsigned char k;
    unsigned long len;
    char *lfn;
    char *info;
    char *p;
    unsigned char j;

    s[32] = 0; // set temporary string length to OSD line length

    scroll_timer = GetTimer(SCROLL_DELAY); // set timer to start name scrolling after predefined time delay
    scroll_offset = 0; // start scrolling from the start

    for (i = 0; i < 8; i++)
    {
        memset(s, ' ', 32); // clear line buffer
        if (i < nDirEntries)
        {
            k = sort_table[i]; // ordered index in storage buffer
            lfn = DirEntryLFN[k]; // long file name pointer
            DirEntryInfo[i][0] = 0; // clear disk number info buffer

            if (lfn[0]) // item has long name
            {
                len = strlen(lfn); // get name length
                info = NULL; // no disk info

                if (!(DirEntry[k].Attributes & ATTR_DIRECTORY)) // if a file
                {
                if (len > 4)
                    if (lfn[len-4] == '.')
                        len -= 4; // remove extension

                info = GetDiskInfo(lfn, len); // extract disk number info

                if (info != NULL)
                   memcpy(DirEntryInfo[i], info, 5); // copy disk number info if present
                }

                if (len > 30)
                    len = 30; // trim display length if longer than 30 characters

                if (i != iSelectedEntry && info != NULL)
                { // display disk number info for not selected items
                    strncpy(s + 1, lfn, 30-6); // trimmed name
                    strncpy(s + 1+30-5, info, 5); // disk number
                }
                else
                    strncpy(s + 1, lfn, len); // display only name
            }
            else  // no LFN
            {
                strncpy(s + 1, (const char*)DirEntry[k].Name, 8); // if no LFN then display base name (8 chars)
                if (DirEntry[k].Attributes & ATTR_DIRECTORY && DirEntry[k].Extension[0] != ' ')
                {
                    p = (char*)&DirEntry[k].Name[7];
                    j = 8;
                    do
                    {
                        if (*p-- != ' ')
                            break;
                    } while (--j);

                    s[1 + j++] = '.';
                    strncpy(s + 1 + j, (const char*)DirEntry[k].Extension, 3); // if no LFN then display base name (8 chars)
                }
            }

            if (DirEntry[k].Attributes & ATTR_DIRECTORY) // mark directory with suffix
                strcpy(&s[25], " <DIR>");
        }
        else
        {
            if (i == 0 && nDirEntries == 0) // selected directory is empty
                strcpy(s, "            No files!");
        }

        OsdWrite(i, s, i == iSelectedEntry); // display formatted line text
    }
}

void _strncpy(char* pStr1, const char* pStr2, size_t nCount)
{
// customized strncpy() function to fill remaing destination string part with spaces

    while (*pStr2 && nCount)
    {
        *pStr1++ = *pStr2++; // copy strings
        nCount--;
    }

    while (nCount--)
        *pStr1++ = ' '; // fill remaining space with spaces
}

// insert floppy image pointed to to by global <file> into <drive>
void InsertFloppy(adfTYPE *drive)
{
    unsigned char i, j;
    unsigned long tracks;

    // calculate number of tracks in the ADF image file
    tracks = file.size / (512*11);
    if (tracks > MAX_TRACKS)
    {
        printf("UNSUPPORTED ADF SIZE!!! Too many tracks: %lu\r", tracks);
        tracks = MAX_TRACKS;
    }
    drive->tracks = (unsigned char)tracks;

    // fill index cache
    for (i = 0; i < tracks; i++) // for every track get its start position within image file
    {
        drive->cache[i] = file.cluster; // start of the track within image file
        for (j = 0; j < 11; j++)
            FileNextSector(&file); // advance by track length (11 sectors)
    }

    // copy image file name into drive struct
    if (file.long_name[0]) // file has long name
        _strncpy(drive->name, file.long_name, sizeof(drive->name)); // copy long name
    else
    {
        strncpy(drive->name, file.name, 8); // copy base name
        memset(&drive->name[8], ' ', sizeof(drive->name) - 8); // fill the rest of the name with spaces
    }

    if (DiskInfo[0]) // if selected file has valid disk number info then copy it to its name in drive struct
    {
        drive->name[16] = ' '; // precede disk number info with space character
        strncpy(&drive->name[17], DiskInfo, sizeof(DiskInfo)); // copy disk number info
    }

    // initialize the rest of drive struct
    drive->status = DSK_INSERTED;
    if (!(file.attributes & ATTR_READONLY)) // read-only attribute
        drive->status |= DSK_WRITABLE;

    drive->cluster_offset = drive->cache[0];
    drive->sector_offset = 0;
    drive->track = 0;
    drive->track_prev = -1;

    // some debug info
    if (file.long_name[0])
        printf("Inserting floppy: \"%s\"\r", file.long_name);
    else
        printf("Inserting floppy: \"%.11s\"\r", file.name);

    printf("file attributes: 0x%02X\r", file.attributes);
    printf("file size: %lu (%lu KB)\r", file.size, file.size >> 10);
    printf("drive tracks: %u\r", drive->tracks);
    printf("drive status: 0x%02X\r", drive->status);
}

/*  Error Message */
void ErrorMessage(char *message, unsigned char code)
{
    if (menustate == MENU_NONE2)
        menustate = MENU_ERROR;

    if (menustate == MENU_ERROR)
    {
        OsdClear();
        OsdWrite(0, "         *** ERROR ***", 1);
        strncpy(s, message, 32);
        s[32] = 0;
        OsdWrite(2, s, 0);

        s[0] = 0;
        if (code)
            sprintf(s, "    #%d", code);

        OsdWrite(4, s, 0);

        OsdEnable(0); // do not disable KEYBOARD
    }
}

void InfoMessage(char *message)
{
    OsdWaitVBL();
    if (menustate != MENU_INFO)
    {
        OsdClear();
        OsdEnable(0); // do not disable keyboard
    }
    OsdWrite(1, message, 0);
    menu_timer = GetTimer(1000);
    menustate = MENU_INFO;
}
