wiretap-retro/MigStorm-ITX/Firmware/ARM Firmware/ASB140501/ARM/src/osd.c

/*
Copyright 2005, 2006, 2007 Dennis van Weeren
Copyright 2008, 2009 Jakub Bednarski

This file is part of Minimig

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
This is the Minimig OSD (on-screen-display) handler.

29-12-2006 - created
30-12-2006 - improved and simplified
-- JB --
2008-10-04 - ARM version
2008-10-26 - added cpu and floppy configuration functions
2008-12-31 - added enable HDD command
2009-02-03 - full keyboard support
2009-06-23 - hires OSD display
2009-08-23 - adapted ConfigIDE() - support for 2 hardfiles
*/

#include "AT91SAM7S256.h"
#include "OSD.h"
#include "hardware.h"
// #include "stdio.h"

// *character font
const unsigned char charfont[256][8] =
{
        {0x00,0x00,0x00,0x00,0x00,0x00,0x00,0x00},         // 0    [0x0]
        {0x55,0x55,0x55,0x55,0x55,0x55,0x55,0x55},         // 1    [0x1]
        {0x2A,0x2A,0x2A,0x2A,0x2A,0x2A,0x2A,0x2A},         // 2    [0x2]
        {0x14,0x14,0x14,0x14,0x14,0x14,0x14,0x14},         // 3    [0x3]
        {0x00,0x00,0x00,0x00,0x00,0x00,0x00,0x00},         // 4    [0x4]
        {0x00,0x00,0x00,0x00,0x00,0x00,0x00,0x00},         // 5    [0x5]
        {0x00,0x00,0x00,0x00,0x00,0x00,0x00,0x00},         // 6    [0x6]
        {0x00,0x00,0x00,0x00,0x00,0x00,0x00,0x00},         // 7    [0x7]
        {0x00,0x00,0x00,0x00,0x00,0x00,0x00,0x00},         // 8    [0x8]
        {0x00,0x00,0x00,0x00,0x00,0x00,0x00,0x00},         // 9    [0x9]
        {0x00,0x00,0x00,0x00,0x00,0x00,0x00,0x00},         // 10   [0xa]
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
      0,  0,  0,  0,  0,  0,  0,  0,  0,  0,  0,  0,  0,  0,  0,  0,
      0,  0,  0,  0,  0,  0,  0,  0,  0,  0,  0,  0,  0,  0,  0,  0,
      0,  0,  0,  0,  0,  0,  0,  0,  0,  0,  0,  0,  0,  0,  0,  0,
      0,  0,  0,  0,  0,  0,  0,  0,  0,  0,  0,  0,  0,  0,  0,  0
};

// write a null-terminated string <s> to the OSD buffer starting at line <n>
void OsdWrite(unsigned char n, char *s, unsigned char invert)
{
    unsigned short i;
    unsigned char b;
    const unsigned char *p;

    // select OSD SPI device
    EnableOsd();

    // select buffer and line to write to
    if (invert)
        SPI(OSDCMDWRITE | 0x10 | n);
    else
        SPI(OSDCMDWRITE | n);

    i = 0;
    // send all characters in string to OSD
    while (1)
    {
        b = *s++;

        if (b == 0) // end of string
            break;

        else if (b == 0x0d || b == 0x0a) // cariage return / linefeed, go to next line
        {
            // increment line counter
            if (++n >= OSDNLINE)
                n = 0;
            // send new line number to OSD
            DisableOsd();
            EnableOsd();
            SPI(OSDCMDWRITE | n);
        }
        else // normal character
        {
            p = &charfont[b][0];
            SPI(*p++);
            SPI(*p++);
            SPI(*p++);
            SPI(*p++);
            SPI(*p++);
            SPI(*p++);
            SPI(*p++);
            SPI(*p++);
            i += 8;
        }
    }
    for (; i < OSDLINELEN; i++) // clear end of line
       SPI(0x00);

    // deselect OSD SPI device
    DisableOsd();
}

void OSD_PrintText(unsigned char line, char *text, unsigned long start, unsigned long width, unsigned long offset, unsigned char invert)
{
// line : OSD line number (0-7)
// text : pointer to null-terminated string
// start : start position (in pixels)
// width : printed text length in pixels
// offset : scroll offset in pixels counting from the start of the string (0-7)
// invert : invertion flag

    const unsigned char *p;

    // select OSD SPI device
    EnableOsd();

    // select buffer and line to write to
    if (invert)
        SPI(OSDCMDWRITE | 0x10 | line);
    else
        SPI(OSDCMDWRITE | line);

    while (start--)
          SPI(0x00);

    if (offset)
    {
        width -= 8 - offset;
        p = &charfont[*text++][offset];
        for (; offset < 8; offset++)
            SPI(*p++);
    }

    while (width > 8)
    {
            p = &charfont[*text++][0];
            SPI(*p++);
            SPI(*p++);
            SPI(*p++);
            SPI(*p++);
            SPI(*p++);
            SPI(*p++);
            SPI(*p++);
            SPI(*p++);
            width -= 8;
    }

    if (width)
    {
        p = &charfont[*text++][0];
        while (width--)
              SPI(*p++);
    }

    DisableOsd();
}

// clear OSD frame buffer
void OsdClear(void)
{
    unsigned short n;

    // select OSD SPI device
    EnableOsd();

    // select buffer to write to
    SPI(OSDCMDWRITE | 0x18);

    // clear buffer
    for (n = 0; n < (OSDLINELEN * OSDNLINE); n++)
        SPI(0x00);

    // deselect OSD SPI device
    DisableOsd();
}

void OsdWaitVBL(void)
{
    unsigned long pioa_old = 0;
    unsigned long pioa = 0;

    while ((~pioa ^ pioa_old) & INIT_B)
    {
        pioa_old = pioa;
        pioa = *AT91C_PIOA_PDSR;
    }
}

// enable displaying of OSD
void OsdEnable(unsigned char mode)
{
    EnableOsd();
    SPI(OSDCMDENABLE | (mode & DISABLE_KEYBOARD));
    DisableOsd();
}

// disable displaying of OSD
void OsdDisable(void)
{
    EnableOsd();
    SPI(OSDCMDDISABLE);
    DisableOsd();
}

void OsdReset(unsigned char boot)
{
    EnableOsd();
    SPI(OSDCMDRST | (boot & 0x01));
    DisableOsd();
}

void ConfigFilter(unsigned char lores, unsigned char hires)
{
    EnableOsd();
    SPI(OSDCMDCFGFLT | ((hires & 0x03) << 2) | (lores & 0x03));
    DisableOsd();
}

void ConfigMemory(unsigned char memory)
{
    EnableOsd();
    SPI(OSDCMDCFGMEM | (memory & 0x0F));
    DisableOsd();
}

void ConfigChipset(unsigned char chipset)
{
    EnableOsd();
    SPI(OSDCMDCFGCHP | (chipset & 0x0F));
    DisableOsd();
}

void ConfigFloppy(unsigned char drives, unsigned char speed)
{
    EnableOsd();
    SPI(OSDCMDCFGFLP | ((drives & 0x03) << 2) | (speed & 0x03));
    DisableOsd();
}

void ConfigScanlines(unsigned char scanlines)
{
    EnableOsd();
    SPI(OSDCMDCFGSCL | (scanlines & 0x0F));
    DisableOsd();
}

void ConfigIDE(unsigned char gayle, unsigned char master, unsigned char slave)
{
    EnableOsd();
    SPI(OSDCMDCFGIDE | (slave ? 4 : 0) | (master ? 2 : 0) | (gayle ? 1 : 0));
    DisableOsd();
}

void ConfigAutofire(unsigned char autofire)
{
    EnableOsd();
    SPI(OSDCMDAUTOFIRE | (autofire & 0x03));
    DisableOsd();
}

// get key status
unsigned char OsdGetCtrl(void)
{
    static unsigned char c2;
    static unsigned long delay;
    static unsigned long repeat;
    static unsigned char repeat2;
    unsigned char c1,c;

    // send command and get current ctrl status
    EnableOsd();
    c1 = SPI(OSDCMDREAD);
    DisableOsd();

    // add front menu button
    if (!CheckButton())
        delay = GetTimer(BUTTONDELAY);
    else if (CheckTimer(delay))
    {
        c1 = KEY_MENU;
        delay = GetTimer(-1);
    }

    // generate normal "key-pressed" event
    c = 0;
    if (c1 != c2)
       c = c1;

    c2 = c1;

    // generate repeat "key-pressed" events
    if (c1 & KEY_UPSTROKE)
    {
        repeat = GetTimer(REPEATDELAY);
    }
    else if (CheckTimer(repeat))
    {
        repeat = GetTimer(REPEATRATE);
        if (c1 == KEY_UP || c1 == KEY_DOWN)
           c = c1;
        repeat2++;
        if (repeat2 == 2)
        {
            repeat2 = 0;
            if (c1 == KEY_PGUP || c1 == KEY_PGDN || c1 == KEY_LEFT || c1 == KEY_RIGHT || GetASCIIKey(c1))
                c = c1;
        }
    }

    return(c);
}

unsigned char GetASCIIKey(unsigned char keycode)
{
    if (keycode & KEY_UPSTROKE)
       return 0;

    return keycode_table[keycode & 0x7F];
}
