wiretap-retro/MigStorm-ITX/Firmware/ARM Firmware/ASB140501/ARM/inc/FPGA.h

void ShiftFpga(unsigned char data);
unsigned char ConfigureFpga(char *CoreName);
void SendFile(fileTYPE *file);
char BootPrint(const char *text);
char BootUpload(fileTYPE *file, unsigned char base, unsigned char size);
void BootExit(void);
void ClearMemory(unsigned long base, unsigned long size);
unsigned char GetFPGAStatus(void);
