wiretap-retro/MigStorm-ITX/Firmware/ARM Firmware/ASB140501/ARM/inc/board.h

#ifndef BOARD_H
#define BOARD_H

//------------------------------------------------------------------------------
//         Headers
//------------------------------------------------------------------------------

#include <stdint.h>
// #include "AT91SAM7S256.h"
#include "printf.h"
#include "stringlight.h"




//---------------------------------------------------------------------------

#endif //#ifndef BOARD_H
