wiretap-retro/MigStorm-ITX/Firmware/ARM Firmware/ASB140501/ARM/inc/errors.h

#define ERROR_NONE 0
#define ERROR_FILE_NOT_FOUND 1
#define ERROR_INVALID_DATA 2
#define ERROR_UPDATE_FAILED 3

extern unsigned char Error;

void FatalError(unsigned long error);
void ErrorMessage(char *message, unsigned char code);
void InfoMessage(char *message);
