wiretap-retro/MigStorm-ITX/Firmware/ARM Firmware/ASB140501/ARM/inc/menu.h

/*menu states*/
enum MENU
{
    MENU_NONE1,
    MENU_NONE2,
    MENU_MAIN1,
    MENU_MAIN2,
    MENU_FILE_SELECT1,
    MENU_FILE_SELECT2,
    MENU_FILE_SELECTED,
    MENU_RESET1,
    MENU_RESET2,
    MENU_SETTINGS1,
    MENU_SETTINGS2,
    MENU_ROMFILE_SELECTED,
    MENU_ROMFILE_SELECTED1,
    MENU_ROMFILE_SELECTED2,
    MENU_SETTINGS_VIDEO1,
    MENU_SETTINGS_VIDEO2,
    MENU_SETTINGS_MEMORY1,
    MENU_SETTINGS_MEMORY2,
    MENU_SETTINGS_CHIPSET1,
    MENU_SETTINGS_CHIPSET2,
    MENU_SETTINGS_DRIVES1,
    MENU_SETTINGS_DRIVES2,
    MENU_SETTINGS_HARDFILE1,
    MENU_SETTINGS_HARDFILE2,
    MENU_HARDFILE_SELECT1,
    MENU_HARDFILE_SELECT2,
    MENU_HARDFILE_SELECTED,
    MENU_HARDFILE_EXIT,
    MENU_HARDFILE_CHANGED1,
    MENU_HARDFILE_CHANGED2,
    MENU_COREFILE_SELECTED,
    MENU_COREFILE_SELECTED1,
    MENU_COREFILE_SELECTED2,
    MENU_MAIN2_1,
    MENU_MAIN2_2,
    MENU_FIRMWARE1,
    MENU_FIRMWARE2,
    MENU_FIRMWARE_UPDATE1,
    MENU_FIRMWARE_UPDATE2,
    MENU_FIRMWARE_UPDATE_ERROR1,
    MENU_FIRMWARE_UPDATE_ERROR2,
    MENU_FIRMWARE_UPDATING1,
    MENU_FIRMWARE_UPDATING2,
    MENU_FIRMWARE_OPTIONS1,
    MENU_FIRMWARE_OPTIONS2,
    MENU_FIRMWARE_OPTIONS_ENABLE1,
    MENU_FIRMWARE_OPTIONS_ENABLE2,
    MENU_FIRMWARE_OPTIONS_ENABLED1,
    MENU_FIRMWARE_OPTIONS_ENABLED2,
    MENU_ERROR,
    MENU_INFO,
    MENU_FPGA1,
    MENU_FPGA2,
};

void InsertFloppy(adfTYPE *drive);
void HandleUI(void);
void PrintDirectory(void);
void ScrollLongName(void);
void ErrorMessage(char *message, unsigned char code);
void InfoMessage(char *message);
